OETSolutions/swc-module/code/tools/check_maintenance_radio.py

#!/usr/bin/env python3
"""Pin the maintenance radio's window-scoped invariants (FR-32, N-15).

**Why this is a gate and not a review step.** `MaintenanceRadio.cpp` is the
THIRD translation unit the host build excludes (beside `EspHal.cpp` and
`UsbLink.cpp`), so no native test compiles it and `test/test_hw` needs the board.
Every property below is therefore asserted by nothing that runs, and each one is
a shape this project has already shipped once:

  1. **Start and stop must pair, and stop must free what start created.**
     FR-32 is a hard rule -- a leaked stack is a device with a live radio while
     it drives a car's steering wheel. `TearDown` therefore frees per-resource
     (one flag each), because the bring-up can bail out partway and a flat
     "free everything" would free something that never came up. Checked here is
     the weaker but checkable half: every flag `TearDown` reads is also SET
     somewhere in the bring-up, so a resource added later cannot be created
     without a corresponding teardown.

  2. **The HTTP handler must reply for EVERY outcome, and must not send a
     status line that can be read as success.** The router's `HttpOutcome`
     carries a status, and `SendOutcome` must call `httpd_resp_set_status` for a
     non-200 -- the app's script checks `r.ok`, so a 401 body sent with a 200
     status line is a refusal the page renders as success (the "reported as
     success" confusion the token gate exists to prevent).

  3. **The failure count must describe the CURRENT window.** It is cleared on
     stop and set on every failed start. The app branches on `ble_failures > 0`
     FIRST when writing the maintenance card, so a sticky count makes every
     later window claim its radio was down while the same frame carries a live
     `page_url` -- a user told there is no setup page with the page right there.

  4. **The failure count must be ASSIGNED, never accumulated.** `+=` makes it a
     running total, which answers a different question than "did this window's
     radio come up" and grows without bound.

  5. **A peer-controlled body length must be clamped in `size_t` before it is
     narrowed.** `httpd_req_t::content_len` is a `size_t`; narrowing it to `int`
     first is the cast-before-bounds family (N-50). A body over 2 GB would read
     as negative, so the stream loop would run zero times and the failure would
     be reported as "install failed" / "empty body" rather than "truncated" --
     the wrong diagnosis for the wrong reason.

  6. **The BLE scheme must be `FREE_BT`, NOT `FREE_BTDM`.** The BTDM handler
     calls `esp_bt_mem_release(ESP_BT_MODE_BTDM)` on deinit, and IDF's own
     contract for that call is that it "cannot be reversed ... you cannot use the
     Bluetooth Controller mode that you have released" (`esp_bt.h`). A second
     `wifi_prov_mgr_init` in a boot therefore re-initialises the controller on
     freed memory and the device REBOOTS -- measured on the bench, every time,
     on the second trip through the window (N-82). The window is a feature a
     user re-enters; a one-shot radio is a broken one.

Each check is structural, which is the point: none can tell a working bring-up
from a broken one (that is the bench's job, per the header), but each pins the
shape that silently rots -- a resource created with no teardown, a reply path
that forgets the status line, a counter that outlives its window, a length cast
before it is bounded, or a scheme that makes the radio one-shot.

Exit codes: 0 clean, 1 a violation, 2 a file could not be found.
"""

import pathlib
import re
import sys

REPO = pathlib.Path(__file__).resolve().parent.parent
RADIO = REPO / "lib" / "Maintenance" / "MaintenanceRadio.cpp"

# Flags that describe this module's own STATE rather than a created resource, and
# are therefore not expected to guard a teardown step. `g_active` is "the radio
# is up"; there is nothing to free for it, and it is cleared for a different
# reason (so `MaintenanceRadioActive` reports down). Named here rather than
# inferred, because inferring "state" from a name is how a real resource quietly
# joins the exclusion list.
_STATE_FLAGS = frozenset({"g_active"})


def _strip_comments(src: str) -> str:
    """Drop // and /* */ so a comment QUOTING the wrong call cannot trip this.

    This codebase documents its invariants in prose, including the wrong version
    of them (that is how several defects were found), so a checker that read
    comments would fail on the documentation of a bug rather than the bug.
    """
    src = re.sub(r"/\*.*?\*/", " ", src, flags=re.DOTALL)
    src = re.sub(r"//[^\n]*", " ", src)
    return src


def _fn_body(src: str, name: str) -> str:
    """The brace-matched body of a function DEFINITION, or '' if not found."""
    m = re.search(
        r"^[A-Za-z_][\w:<>,\s\*&]*\b" + re.escape(name) + r"\s*\([^;{]*\)\s*\{",
        src,
        flags=re.MULTILINE,
    )
    if not m:
        return ""
    start = src.index("{", m.start())
    depth = 0
    for i in range(start, len(src)):
        if src[i] == "{":
            depth += 1
        elif src[i] == "}":
            depth -= 1
            if depth == 0:
                return src[start : i + 1]
    return ""


def check_teardown_pairs_the_bringup(src: str):
    """(1) Every flag TearDown clears must be SET by the bring-up.

    A resource that is created and never torn down is FR-32's exact violation,
    and the host build cannot see it -- there is no test that compiles this file.
    The flag names are read from `TearDown` itself rather than a second list, so
    a resource added to the teardown is what drives the check.
    """
    problems = []
    teardown = _fn_body(src, "TearDown")
    if not teardown:
        return ["TearDown not found in MaintenanceRadio.cpp"]

    # `<flag> = false;` inside TearDown names the resources it owns. A state flag
    # is not one of them -- see `_STATE_FLAGS`.
    flags = sorted(
        set(re.findall(r"\b(g_\w+)\s*=\s*false\s*;", teardown)) - _STATE_FLAGS
    )
    if not flags:
        problems.append(
            "TearDown clears no resource flag; it frees by flag, so a flagless "
            "teardown is a flat 'free everything' that frees resources a partial "
            "bring-up never created."
        )

    # The pointer handles are the other half: they are nulled, not flag-cleared.
    handles = sorted(set(re.findall(r"\b(g_\w+)\s*=\s*nullptr\s*;", teardown)))

    creation = src
    for flag in flags:
        # A flag is "set" if it appears on the left of a true-assignment or is
        # declared true, anywhere OUTSIDE the teardown.
        outside = src.replace(teardown, " ")
        if not re.search(r"\b" + re.escape(flag) + r"\s*=\s*true\s*;", outside):
            problems.append(
                f"TearDown clears {flag}, but nothing sets it true outside the "
                f"teardown. Freeing by a flag that is never set means the "
                f"resource it guards is either never freed (leaked radio, FR-32) "
                f"or the flag is dead."
            )
    for h in handles:
        if not re.search(r"\b" + re.escape(h) + r"\s*=\s*[^=]", creation.replace(teardown, " ")):
            problems.append(
                f"TearDown nulls {h}, but nothing else assigns it. The handle it "
                f"guards is then never created or never released."
            )
    return problems


def check_every_reply_sets_its_status(src: str):
    """(2) A non-200 reply must set the status line."""
    problems = []
    body = _fn_body(src, "SendOutcome")
    if not body:
        return ["SendOutcome not found in MaintenanceRadio.cpp"]
    if "httpd_resp_set_status" not in body:
        problems.append(
            "SendOutcome never calls httpd_resp_set_status. The app's script "
            "checks `r.ok`, so a 401/404/500 body sent with the default 200 "
            "status line is a refusal the page renders as success -- the exact "
            "confusion the token gate exists to prevent."
        )
    if "o.status" not in body:
        problems.append(
            "SendOutcome does not read the outcome's status, so every reply goes "
            "out as the default response."
        )
    return problems


def check_the_failure_count_is_window_scoped(src: str):
    """(3)+(4) Cleared on stop, set (not accumulated) on a failed start."""
    problems = []

    stop = _fn_body(src, "MaintenanceRadioStop")
    if not stop:
        problems.append("MaintenanceRadioStop not found in MaintenanceRadio.cpp")
    elif not re.search(r"\bg_failures\s*=\s*0\s*;", stop):
        problems.append(
            "MaintenanceRadioStop does not clear g_failures. The count answers "
            "'did THIS window's radio come up', and the app branches on it FIRST "
            "when writing the maintenance card -- so a value left standing makes "
            "every later window say its radio was down while the same frame "
            "carries a live page_url."
        )

    start = _fn_body(src, "MaintenanceRadioStart")
    if not start:
        problems.append("MaintenanceRadioStart not found in MaintenanceRadio.cpp")
    else:
        # Any mutation of the count, prefix-increment included, so `++g_failures`
        # cannot slip past a check that only looked for a trailing operator.
        mutated = re.findall(r"\bg_failures\s*(\+\+|--|\+=|-=|=)", start)
        mutated += ["++"] * len(re.findall(r"(?:\+\+|--)\s*g_failures\b", start))
        if not mutated:
            problems.append(
                "MaintenanceRadioStart never records a failure, so a window whose "
                "radio did not come up is indistinguishable from a working one."
            )
        for op in mutated:
            if op in ("++", "--", "+=", "-="):
                problems.append(
                    f"MaintenanceRadioStart mutates g_failures with '{op}'. It is "
                    f"a state (0 = this window's radio is up), not a running "
                    f"total: accumulating answers a different question and grows "
                    f"without bound. Assign 1 on a failure."
                )
    return problems


def check_body_lengths_are_clamped_before_narrowing(src: str):
    """(5) `content_len` (a size_t) must be bounded in `size_t`, not `int`."""
    problems = []
    # Any line that names content_len AND casts it to int ON THE SAME line, before
    # any comparison against a constant -- i.e. `static_cast<int>(...content_len)`
    # appearing to the LEFT of a `<`/`<=`/`?`.
    for m in re.finditer(r"[^\n]*content_len[^\n]*", src):
        line = m.group(0)
        cast = line.find("static_cast<int>")
        if cast < 0:
            continue
        # Is the cast applied directly to content_len (rather than to something
        # already clamped)? Look at the text right after the cast's '('.
        after = line[cast + len("static_cast<int>") :].lstrip()
        if after.startswith("(req->content_len") or after.startswith("req->content_len") \
                or after.startswith("(content_len"):
            problems.append(
                "a body length is narrowed with `static_cast<int>(...content_len)` "
                "before it is bounded. clamp in `size_t` first and cast the CLAMPED "
                "value, or a body over 2 GB reads as negative and is reported as "
                "'empty'/'install failed' rather than 'too long' (N-50)."
            )
    return problems


def check_the_ble_scheme_is_not_one_shot(src: str):
    """(6) The scheme must not release the BTDM pool that it then needs again."""
    problems = []
    if "scheme_event_handler" not in src:
        problems.append(
            "no `scheme_event_handler` is set on wifi_prov_mgr_config_t; the "
            "default releases nothing, which leaks classic-BT memory this part "
            "cannot spare (spec 9.2)."
        )
        return problems
    if "WIFI_PROV_SCHEME_BLE_EVENT_HANDLER_FREE_BTDM" in src:
        problems.append(
            "the BLE scheme is FREE_BTDM, whose deinit calls "
            "esp_bt_mem_release(ESP_BT_MODE_BTDM) -- a ONE-WAY release per IDF's "
            "own contract. The second wifi_prov_mgr_init in a boot re-inits the "
            "controller on freed memory and REBOOTS the device, so the "
            "maintenance window would be one-shot (N-82). Use FREE_BT: it "
            "releases classic BT at init and leaves the BTDM pool reserved."
        )
    if "WIFI_PROV_SCHEME_BLE_EVENT_HANDLER_FREE_BT" not in src:
        problems.append(
            "the BLE scheme is not FREE_BT, so classic-BT memory may not be "
            "released at all -- on a 4 MB/no-PSRAM part that is memory the "
            "design cannot spare (spec 9.2)."
        )
    return problems


def main() -> int:
    if not RADIO.exists():
        print(f"FAIL: {RADIO} not found", file=sys.stderr)
        return 2
    src = _strip_comments(RADIO.read_text(encoding="utf-8"))

    problems = []
    problems += check_teardown_pairs_the_bringup(src)
    problems += check_every_reply_sets_its_status(src)
    problems += check_the_failure_count_is_window_scoped(src)
    problems += check_body_lengths_are_clamped_before_narrowing(src)
    problems += check_the_ble_scheme_is_not_one_shot(src)

    if problems:
        print("maintenance-radio guard FAILED:", file=sys.stderr)
        for p in problems:
            print(f"  - {p}", file=sys.stderr)
        return 1

    print("maintenance-radio guard: OK")
    print("  TearDown frees by a flag the bring-up sets (FR-32)")
    print("  every reply sets its status line, so no refusal reads as success")
    print("  the failure count is window-scoped and assigned, never accumulated")
    print("  peer body lengths are clamped in size_t before any narrowing cast")
    print("  the BLE scheme is re-enterable (FREE_BT, not the one-shot FREE_BTDM)")
    return 0


if __name__ == "__main__":
    sys.exit(main())
