OETSolutions/swc-module/code/tools/bench_ota_corrupt.py

#!/usr/bin/env python3
"""Prove the USB-OTA path REFUSES a corrupt image and does not brick the device.

**Why this is a script and not a unit test.** The verification gate
(`ImageVerify`) is host-testable and IS tested, but the thing the HANDOFF asks to
prove only exists on hardware: that a corrupt image pushed over the real USB-OTA
path (`esp_ota_begin` / `esp_ota_write` / `esp_ota_end` into the NON-RUNNING
slot) is refused, and that the device **keeps running** afterwards. The failure
this guards against is the worst kind: a bad write that commits, so the device
reboots into a slot that does not work and needs a physical recovery. That can
only be settled with the part in hand.

The test, in order, on the live device:

  1. read the baseline: `uptime_ms`, `heap_free`, `config_state`
  2. `ota_begin` with the TRUE size and the TRUE sha256 of a real build
  3. stream the image with ONE byte flipped inside the payload
  4. `ota_end` -> must be a `nack` (NOT an ack), and the reason must be the
     verification one, not a transport accident
  5. re-read `uptime_ms` and re-issue a command: the device must NOT have
     rebooted (uptime must not have reset) and must still answer
  6. read the two app-slot headers back and confirm the RUNNING slot is
     untouched, so a refused image left no partial state behind

Exit codes: 0 the device refused the corrupt image and stayed up, 1 the device
ACCEPTED it (a real defect), 2 usage/port error.
"""

import argparse
import base64
import hashlib
import json
import os
import subprocess
import sys
import time

try:
    import serial
except ImportError:  # pragma: no cover
    print("ERROR: pyserial not available; run under the PlatformIO penv python.",
          file=sys.stderr)
    sys.exit(2)

CHUNK = 512  # kConfigWireChunkBytes


class Link:
    def __init__(self, port, timeout=2.0):
        self.ser = serial.Serial(port, 115200, timeout=0.25)
        self.ser.dtr = True
        self.timeout = timeout
        self.seq = 0
        self.pending = b""
        time.sleep(0.4)
        self.ser.reset_input_buffer()

    def close(self):
        try:
            self.ser.close()
        except Exception:
            pass

    def request(self, **frame):
        self.seq += 1
        seq = self.seq
        frame = {"v": 1, "seq": seq, **frame}
        self.ser.write((json.dumps(frame, separators=(",", ":")) + "\n").encode())
        self.ser.flush()
        deadline = time.time() + self.timeout
        while time.time() < deadline:
            try:
                self.pending += self.ser.read(4096)
            except Exception:
                break
            while b"\n" in self.pending:
                line, self.pending = self.pending.split(b"\n", 1)
                line = line.strip()
                if not line:
                    continue
                try:
                    msg = json.loads(line)
                except json.JSONDecodeError:
                    continue
                if msg.get("for_seq") == seq and msg.get("type") in ("ack", "nack"):
                    return msg.get("type"), msg
        return None, None

    def status(self, seconds=2.0):
        """Send a `ping` (spec 4.3: "Liveness; FW answers `status`") and return
        the status frame it produces, or None.

        **Draining alone is not enough.** The device emits `status` on connect and
        in response to a ping, not continuously -- so a passive read can sit
        forever on a healthy device and report it dead. Asking is what makes the
        liveness check meaningful.
        """
        self.seq += 1
        seq = self.seq
        self.ser.write((json.dumps({"v": 1, "seq": seq, "type": "ping"},
                                   separators=(",", ":")) + "\n").encode())
        self.ser.flush()
        deadline = time.time() + seconds
        last = None
        while time.time() < deadline:
            try:
                self.pending += self.ser.read(4096)
            except Exception:
                break
            while b"\n" in self.pending:
                line, self.pending = self.pending.split(b"\n", 1)
                if not line.strip():
                    continue
                try:
                    msg = json.loads(line)
                except json.JSONDecodeError:
                    continue
                if msg.get("type") == "status":
                    last = msg
        return last


def read_slot_header(esptool, port, offset):
    """Return the first 32 bytes of a flash region, or None on failure."""
    out = f"/tmp/swc_slot_{offset:x}.bin"
    try:
        subprocess.run(
            [esptool, "--chip", "esp32s3", "--port", port,
             "--before", "no_reset", "--after", "no_reset",
             "read_flash", hex(offset), "0x20", out],
            check=True, capture_output=True, timeout=40)
        return open(out, "rb").read()
    except Exception as e:
        print(f"  (could not read slot {hex(offset)}: {e})")
        return None
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
