OETSolutions/swc-module/code/tools/test_gen_contract.py

"""Tests for the generated contract.

Run: `cd code/tools && python3 -m pytest test_gen_contract.py -v`

The point of these is not that the generators run. It is that every fact with a
SECOND home is asserted to still agree with its first, because that is how this
project's defects have actually happened: two spellings of one list, one of them
stale, with nothing comparing them.
"""

import pathlib
import re
import subprocess
import sys

import pytest

HERE = pathlib.Path(__file__).resolve().parent
CODE = HERE.parent

import contract_schema  # noqa: E402


def _read(rel):
    return (CODE / rel).read_text()


def test_action_kinds_are_contiguous_from_zero():
    # A kind's ordinal is its in-memory value on each side, so a gap would be a
    # value nothing defines. (Action ids 1-63 are a different thing and do not
    # exist at all; the wire carries the kind NAME, per spec 3.6.)
    ordinals = sorted(k.ordinal for k in contract_schema.ACTION_KINDS)
    assert ordinals == list(range(len(ordinals))), "kind ordinals must have no gaps"


def test_there_are_exactly_the_eleven_spec_kinds():
    # Spec 3.6's table. A kind added here without a spec entry is a name the app
    # can send and the firmware has no behavior for.
    assert len(contract_schema.ACTION_KINDS) == 11
    assert contract_schema.ACTION_KINDS[0].name == "NONE"


def _firmware_action_kind_enumerators():
    """Parsed from ConfigModel.h -- the firmware's own declaration order."""
    text = _read("lib/Config/ConfigModel.h")
    body = text.split("enum class ActionKind : uint8_t {", 1)[1].split("};", 1)[0]
    return [w.strip() for w in body.replace("\n", " ").split(",") if w.strip()]
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
